DanNduati/Final-year-project/budget/project.jpeg

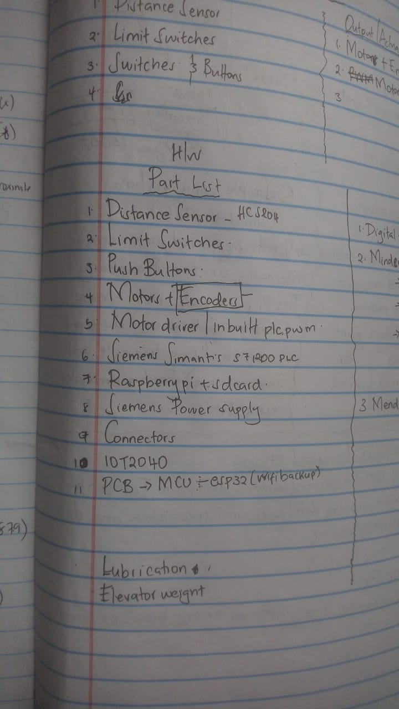
budget/project.jpeg
