DanNduati/Final-year-project/images/mindconnectiotpackageprice.png

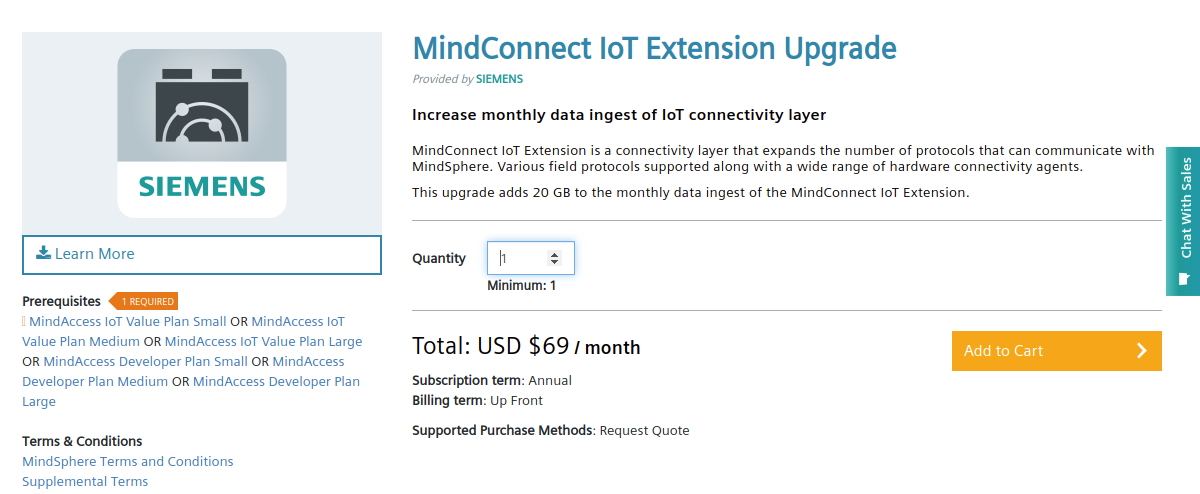
images/mindconnectiotpackageprice.png
