DanNduati/Final-year-project/images/report/firbase_1.png

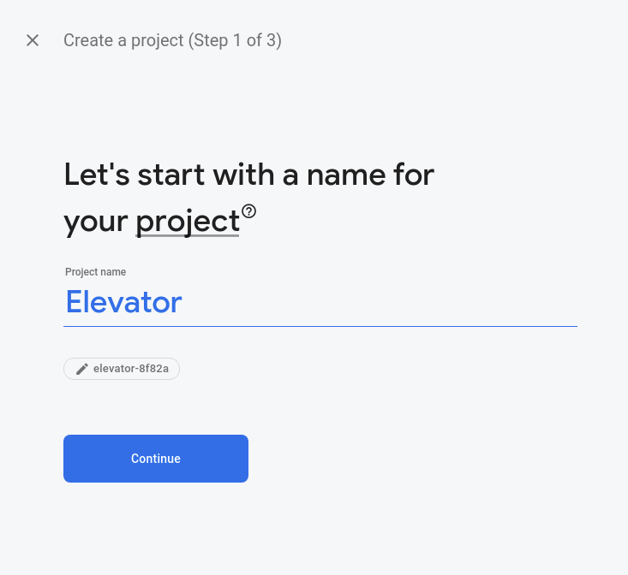
images/report/firbase_1.png
