DanNduati/Final-year-project/images/report/firebase_4.png

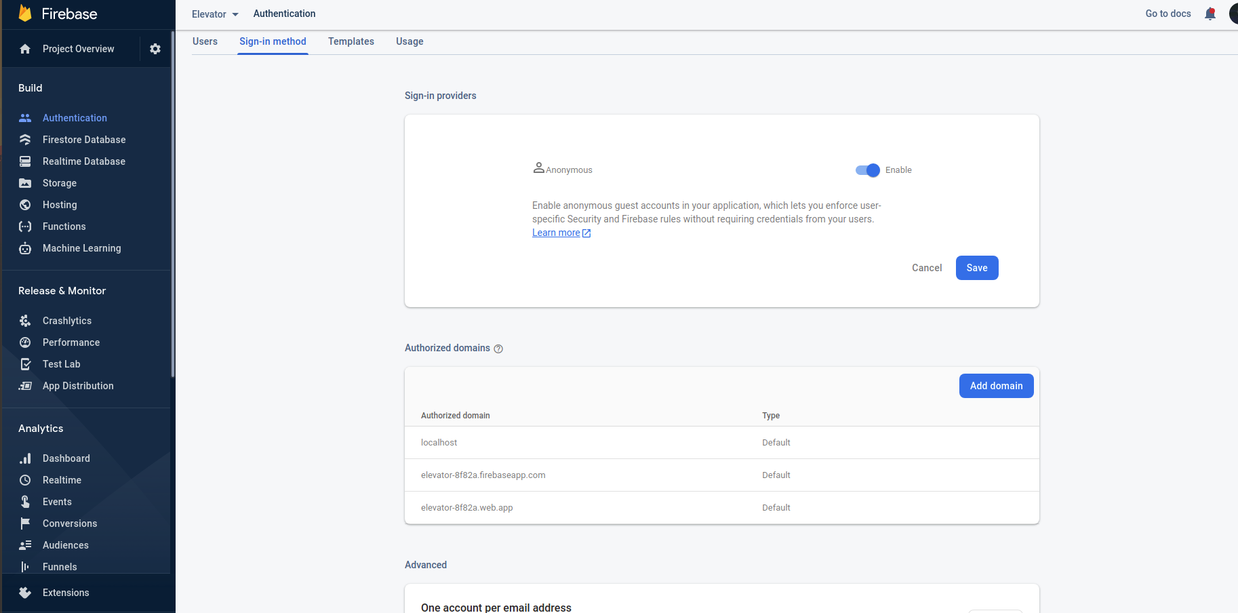
images/report/firebase_4.png
