DanNduati/Final-year-project/onboarding/images/1_create_basic_asset.png

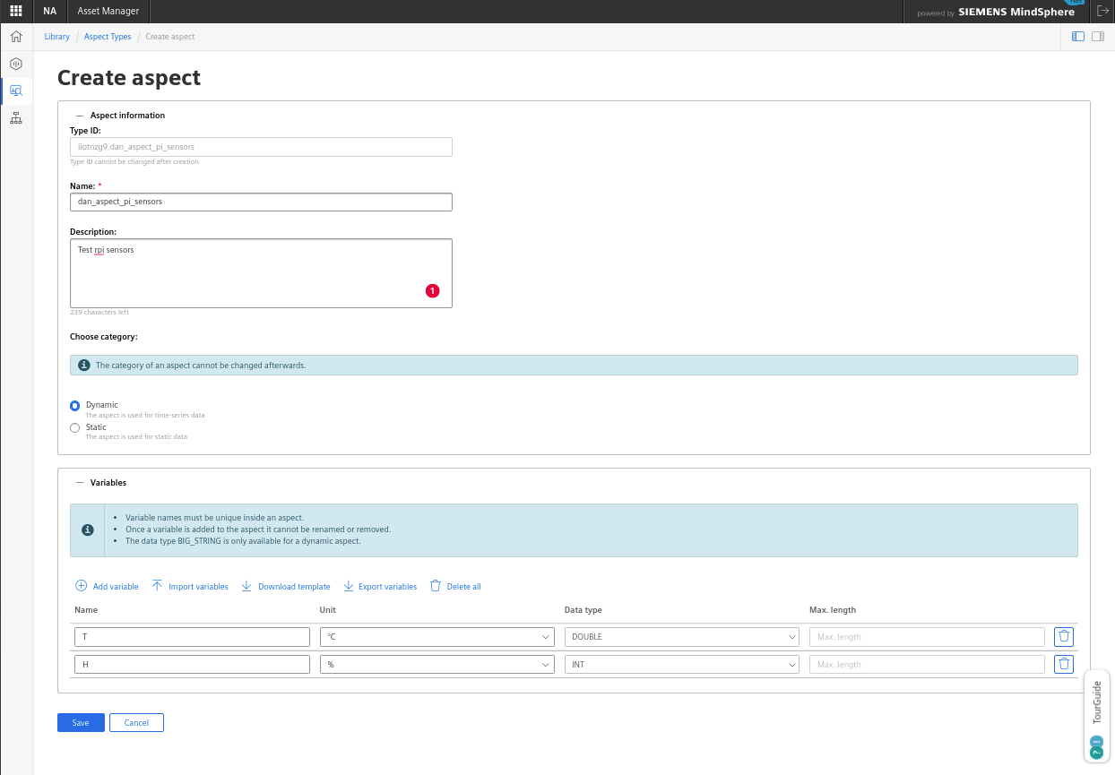
onboarding/images/1_create_basic_asset.png
