DanNduati/Final-year-project/onboarding/images/Screenshot from 2021-07-28 14-48-39.png

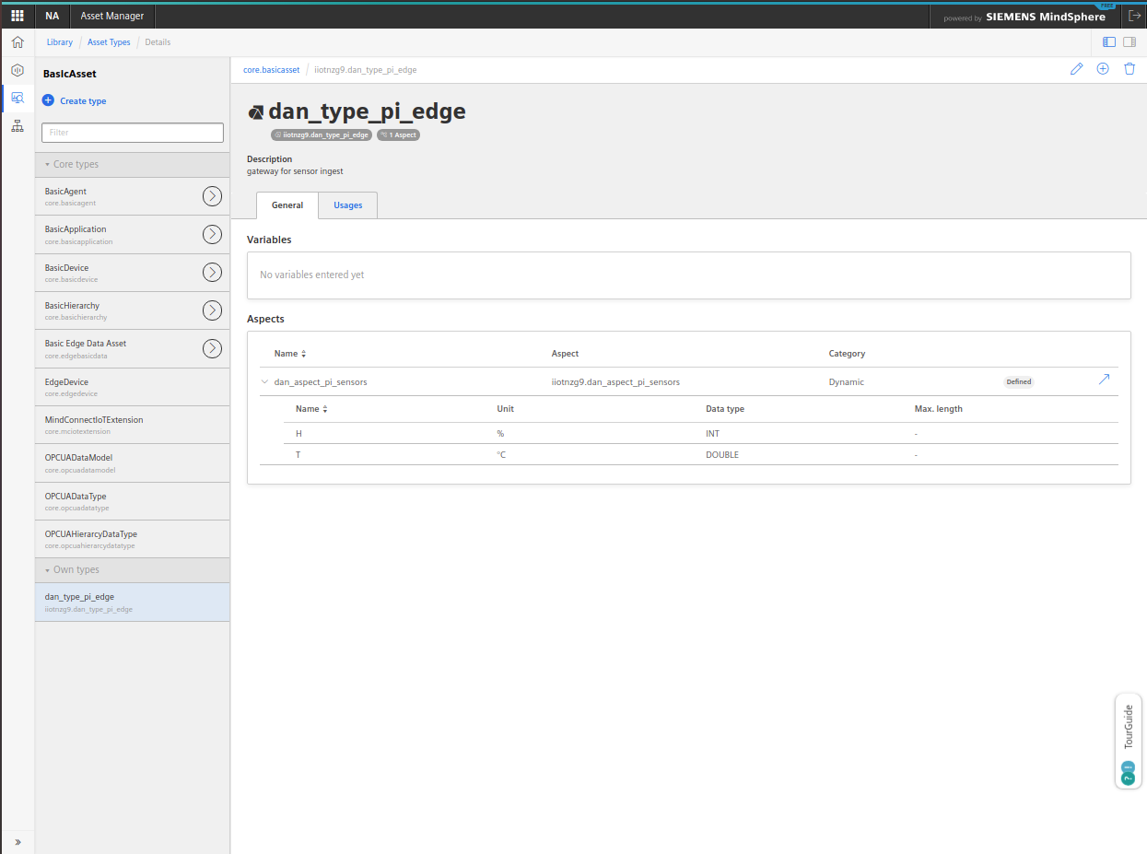
onboarding/images/Screenshot from 2021-07-28 14-48-39.png
