DanNduati/Final-year-project/twin/dist/client/models/elevator/textures/Material_0_baseColor.png

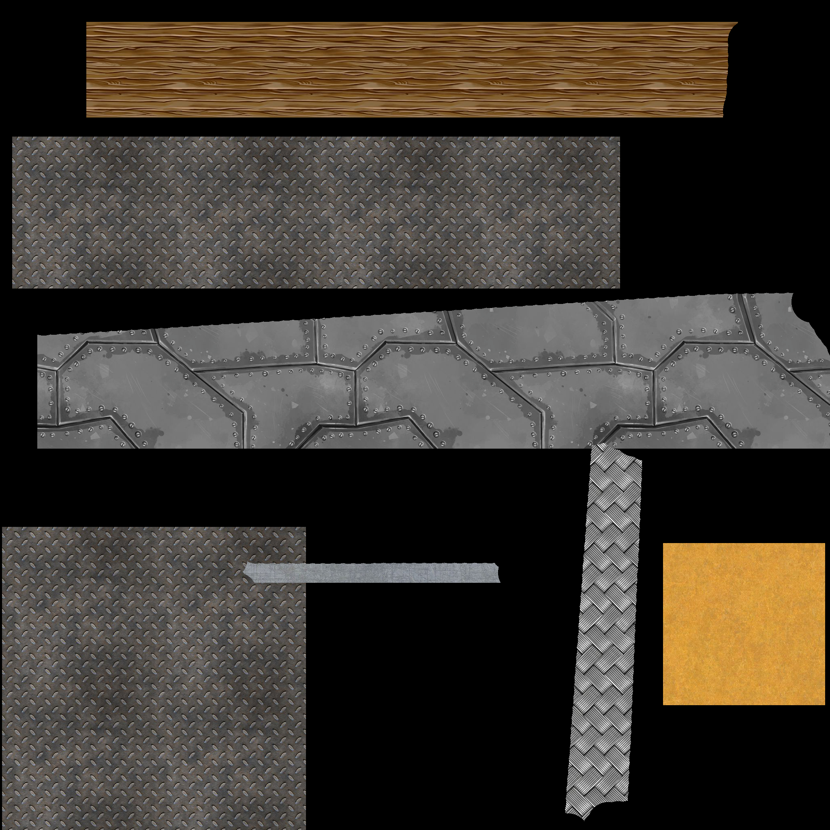
twin/dist/client/models/elevator/textures/Material_0_baseColor.png
